adam-dev-hub/eausure-all/EauSure_3D/Gateway_Node/preview/gateway_shell.png

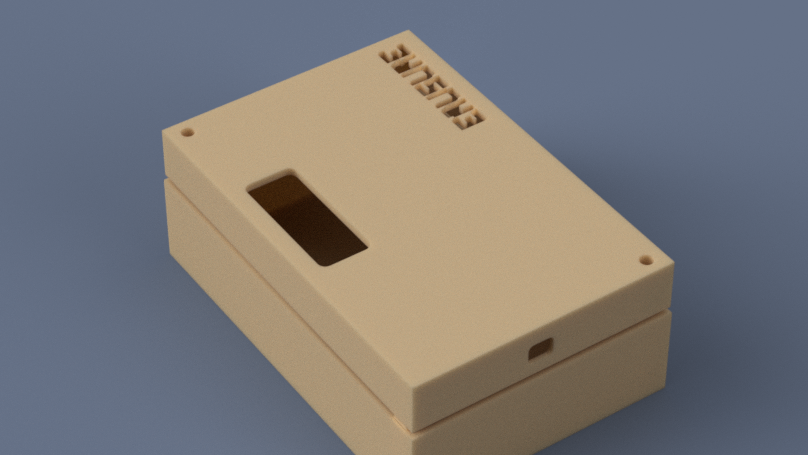
EauSure_3D/Gateway_Node/preview/gateway_shell.png
