adam-dev-hub/eausure-all/EauSure_3D/IoT_Node/exports/previews/eausure-buoy-shell.png

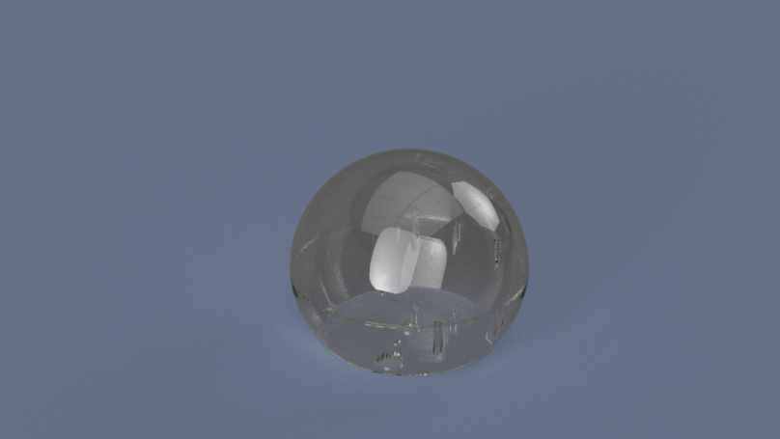
EauSure_3D/IoT_Node/exports/previews/eausure-buoy-shell.png
