adam-dev-hub/eausure-all/EauSure_3D/IoT_Node/exports/previews/eausure-buoy-up-shell.png

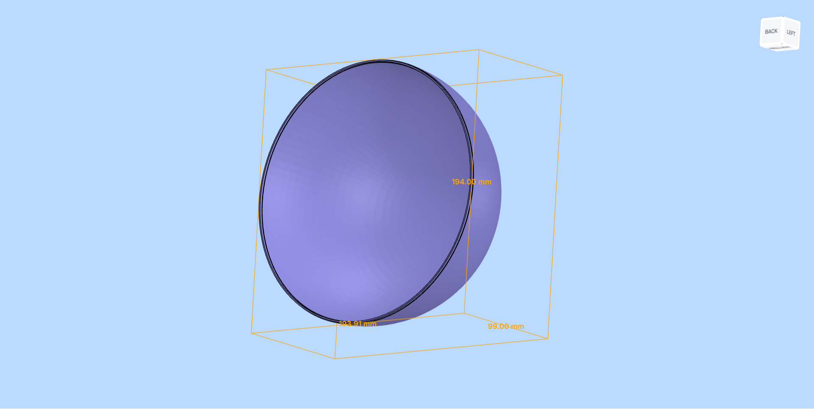
EauSure_3D/IoT_Node/exports/previews/eausure-buoy-up-shell.png
