adam-dev-hub/eausure-all/EauSure_User_MobileApp/assets/illustrations/tds-info.png

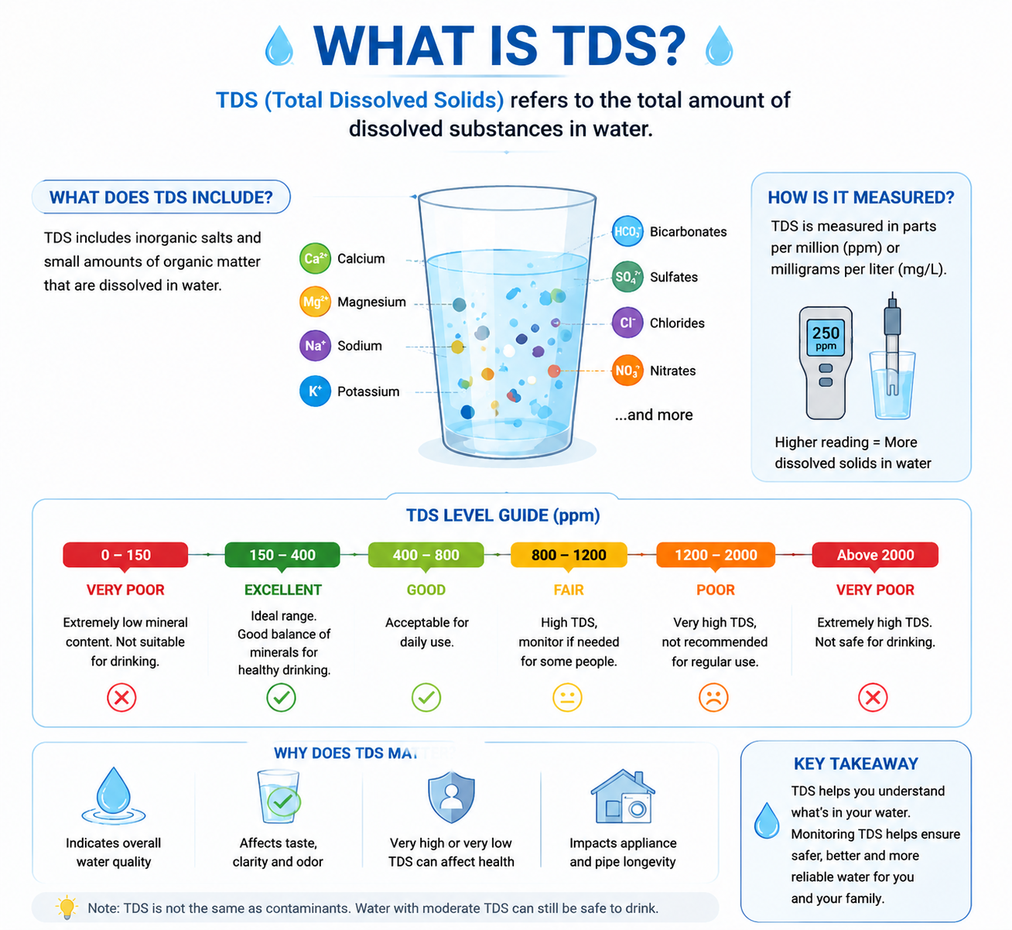
EauSure_User_MobileApp/assets/illustrations/tds-info.png
