adam-dev-hub/eausure-all/EauSure_User_MobileApp/assets/illustrations/temperature-info.png

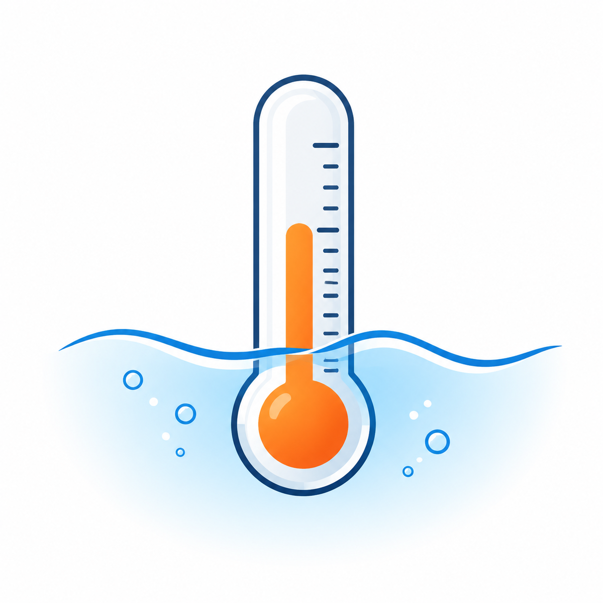
EauSure_User_MobileApp/assets/illustrations/temperature-info.png
