adam-dev-hub/eausure-all/EauSure_User_MobileApp/assets/illustrations/turbidity-info.png

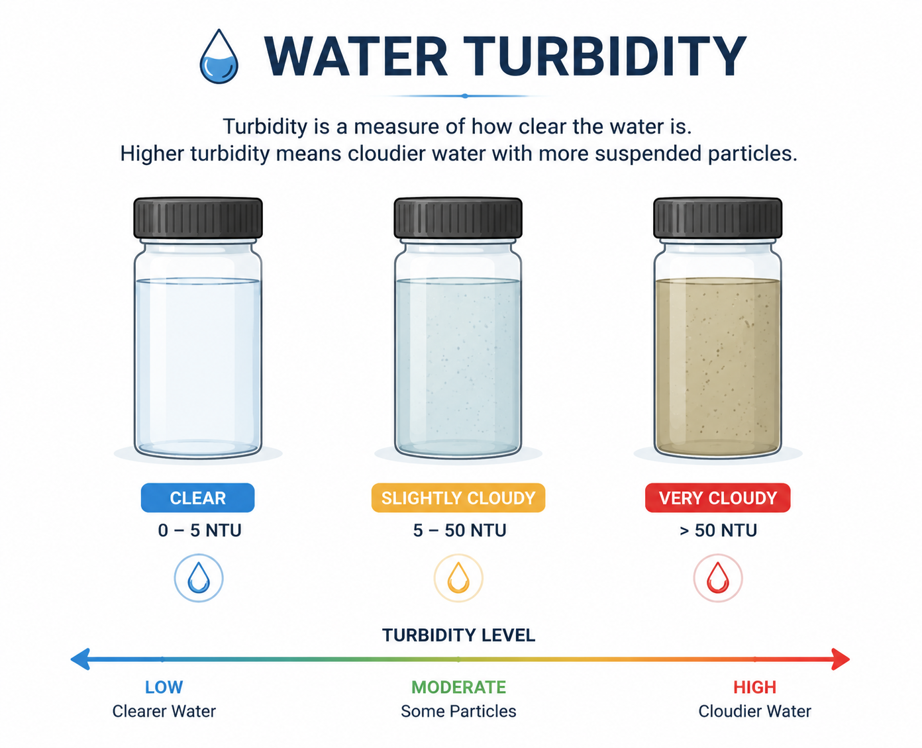
EauSure_User_MobileApp/assets/illustrations/turbidity-info.png
