adam-dev-hub/eausure-all/EauSure_User_MobileApp/assets/onboarding/slide-frame-1.jpg

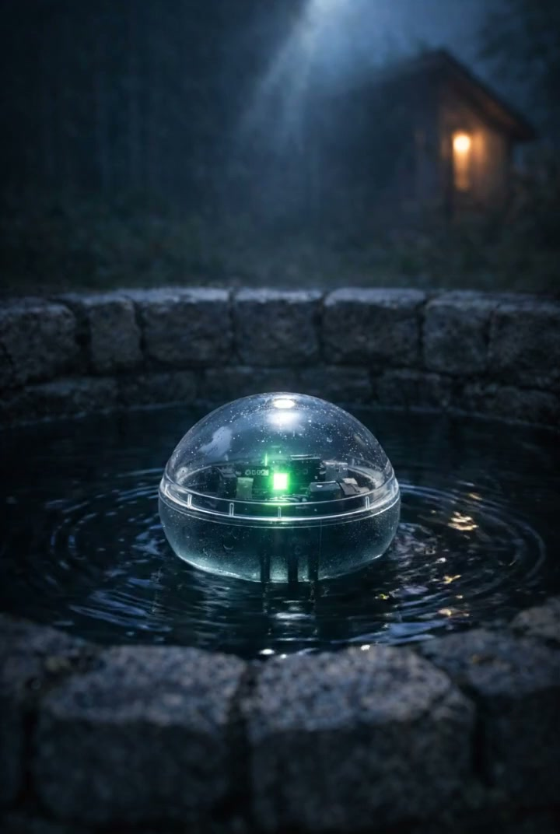
EauSure_User_MobileApp/assets/onboarding/slide-frame-1.jpg
