adam-dev-hub/eausure-all/EauSure_PCB/exports/board/eausure-measurement-node-board-gerber.png

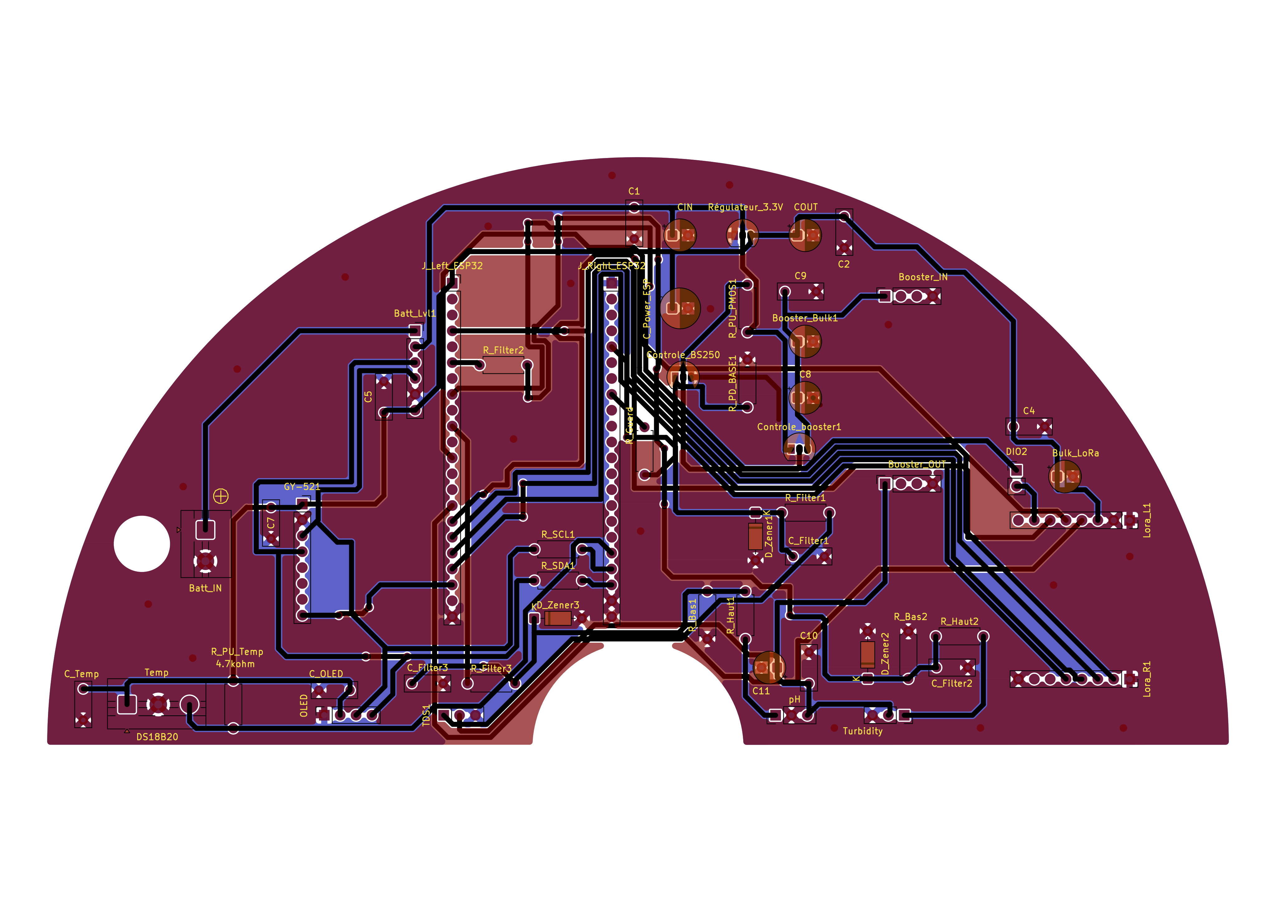
EauSure_PCB/exports/board/eausure-measurement-node-board-gerber.png
