adam-dev-hub/eausure-all/EauSure_PCB/exports/board/eausure-measurement-node-board-preview-1.png

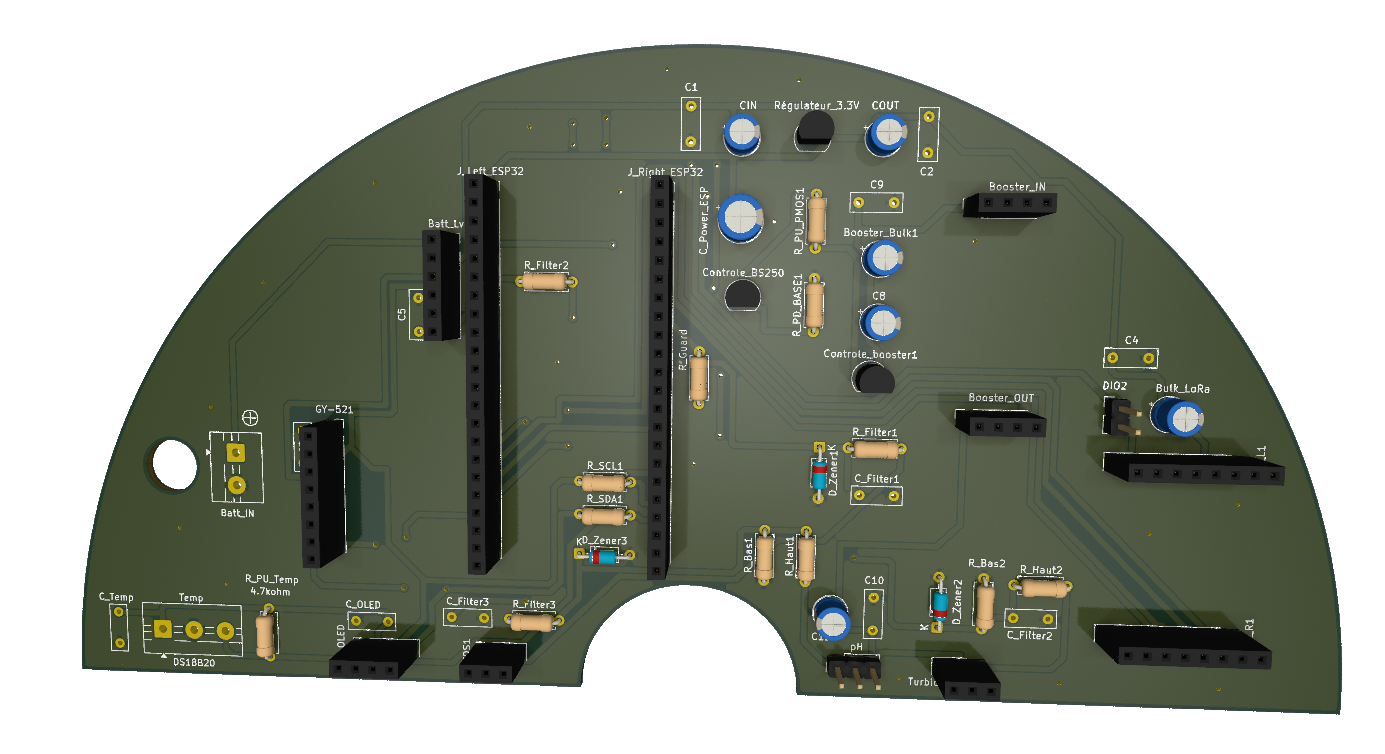
EauSure_PCB/exports/board/eausure-measurement-node-board-preview-1.png
