adam-dev-hub/eausure-all/EauSure_PCB/exports/schematics/eausure-measurement-node-simplified.png

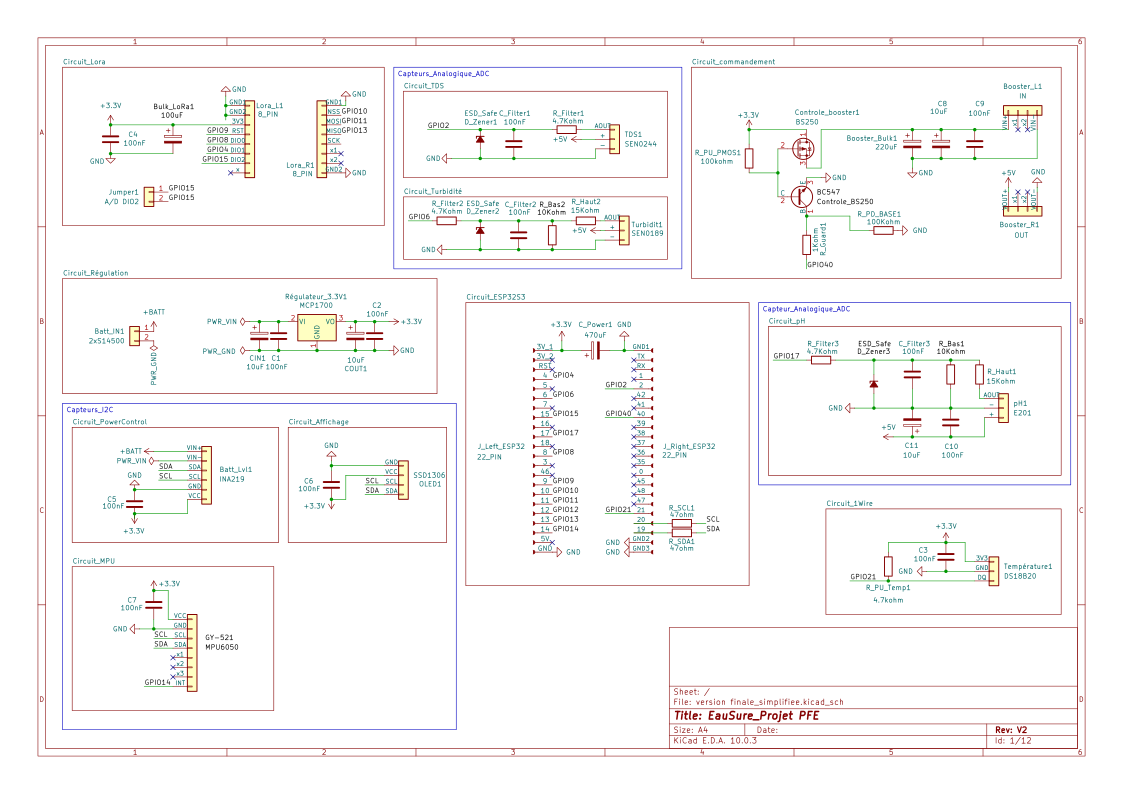
EauSure_PCB/exports/schematics/eausure-measurement-node-simplified.png
