adam-dev-hub/eausure-all/EauSure_Firmware/Gateway_Node/lora_radio.h

#pragma once

#include <Arduino.h>
#include <LoRa.h>
#include <SPI.h>
#include "config.h"
#include "app_state.h"

// =====================================================
// LoRa init
// =====================================================
bool initLoRa();

// =====================================================
// Gateway → IoT  typed command TX functions
//
//  sendActivate()      — boot handshake, activates node
//  sendMeasureReq()    — request fresh sensor reading
//  sendHeartbeatReq()  — lightweight liveness ping
// =====================================================
bool isGatewayCommandInFlight();
bool sendActivate();
bool sendMeasureReq();
bool sendHeartbeatReq();
bool sendSetConfig(float shakeThresholdG, bool shakeEnabled);
bool sendUnpair();
bool sendSleepReq(uint32_t sleepDurationSec);
bool sendFuotaBegin(uint32_t sessionId, uint32_t totalSize, uint16_t chunkSize, uint16_t totalChunks, const String& version, const String& md5);
bool sendFuotaChunk(uint32_t sessionId, uint32_t chunkIndex, const uint8_t* data, uint16_t len);
bool sendFuotaEnd(uint32_t sessionId, uint32_t totalSize, uint16_t totalChunks);
bool sendFuotaCommit(uint32_t sessionId);

// =====================================================
// Queued Configuration (Class A workaround)
// =====================================================
void queueSetConfig(float shakeThresholdG, bool shakeEnabled);
bool hasPendingConfig();
bool sendPendingConfig();

// =====================================================
// Transport-level ACK sent to IoT node
// =====================================================
bool sendAck(uint32_t seq);

// =====================================================
// Incoming DATA frame parser
// Called from loop() when a DATA frame arrives.
// Handles MEASURE_RESP and SHAKE_ALERT (both type=0x01).
// =====================================================
bool parseAndDispatchDataFrame(const uint8_t *frame, size_t frameLen,
                                int rssi, float snr);

// =====================================================
// Incoming IoT→GW typed frame parser
// Called from loop() for non-DATA frames (ACTIVATE_OK, HB_ACK).
// =====================================================
bool parseAndDispatchTypedFrame(const uint8_t *frame, size_t frameLen, int rssi, float snr);
