adam-dev-hub/eausure-all/EauSure_Firmware/Gateway_Node/mqtt_gateway.h

#pragma once
#include <Arduino.h>

namespace MqttGateway {

void begin();
void loop();

bool isConnected();
void setExclusiveTlsWindow(bool enabled);

bool publishEvent(const String& eventName, const String& payloadJson);
bool publishCandidateFound(const String& nodeId, const String& nodeName, const String& bleMac);
bool publishScanComplete(bool found);
bool publishPairingFailed(const String& nodeId, const String& reason);

String commandTopic();
String eventTopic();

} // namespace MqttGateway
