adam-dev-hub/eausure-all/EauSure_Firmware/Gateway_Node/wifi_manager.h

#ifndef WIFI_MANAGER_H
#define WIFI_MANAGER_H

#include <WiFi.h>
#include <HTTPClient.h>
#include <WiFiClientSecure.h>
#include "config.h"

namespace WiFiManager {
    enum class SubmitResult : uint8_t {
        Success = 0,
        RetryableError,
        RateLimited,
    };

    // Initialize WiFi connection with runtime credentials
    bool init(const char* ssid, const char* password);

    // Retry using the last runtime credentials
    bool reconnect();

    // Check if connected
    bool isConnected();

    // Call API to unprovision gateway
    bool unprovisionGateway();

    // Download a firmware or asset file to the SD card over HTTPS.
    bool downloadFileToSd(
        const String& url,
        const char* sdPath,
        size_t expectedSize,
        String* errorOut = nullptr
    );

    // Submit sensor data to API
    SubmitResult submitSensorData(
        const char* nodeId,
        const char* gatewayHardwareId,
        uint32_t seq,
        uint8_t battery,
        float voltage,
        uint16_t current,
        float pH,
        uint8_t phStatus,
        uint16_t tds,
        uint8_t tdsStatus,
        float turbidity,
        uint8_t turbidityStatus,
        float waterTemp,
        float moduleTemp,
        float esp32Temp,
        const char* errorMsg,
        int8_t rssi,
        float snr,
        int* httpStatusOut = nullptr,
        const char* firmwareVersion = nullptr
    );

    // Get WiFi status string
    const char* getStatusString();

    // Get signal strength
    int8_t getSignalStrength();

    // Useful helpers
    String getIP();
    String getMacAddress();
}

#endif
